TVavrinec/AHS-Automaticke_Herni_Stanoviste/text/sablona-obhaj.pdf

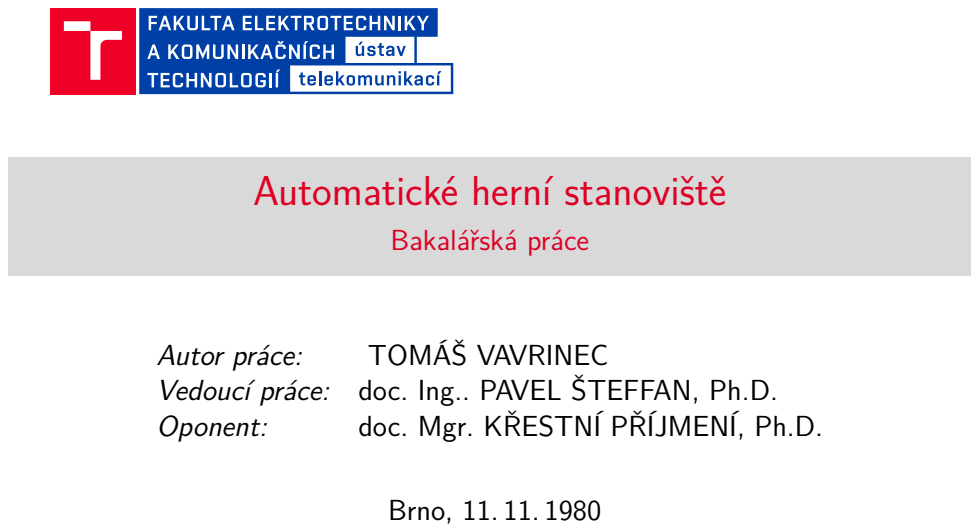
[picture p24: page 1]
Bakalářská práce; Autor práce:; TOMÁŠ VAVRINEC; Oponent:; doc. Mgr. KŘESTNÍ PŘÍJMENÍ, Ph.D.; Brno, 11. 11. 1980

Automatické herní stanoviště

Vedoucí práce: doc. Ing.. PAVEL ŠTEFFAN, Ph.D.

## Cíle práce

Nastudovat
Popsat
nastudované
Implementovat
nastudované
nové
Porovnat a vyhodnotit
výsledky
Tomáš Vavrinec | Automatické herní stanoviště | 1 / 7

## Klíčové nástroje

### Pro práci je klíčový Eulerův vzorec

e

jx = cos x + j sin x

Eulerova identita je speciálním případem tohoto vzorce, jestliže dosadíme x = π :

### Eulerova identita

e

jπ = cos π + j sin π,

odkud vyplývá
e

jπ + 1 = 0.

## Plošný spoj

Obrázek znázorňuje model:

Deska
Součástky
Signály
Napájení

## Výsledky

Tab. 1: Výsledky měření mobilních sítí

Technologie | Rychlost stahování [kB/s] Rychlost nahrávání [kB/s]
GPRS (2,5G) | 7,2 | 3,6
UMTS 3G | 48 | 48
HSPA (3,5G) | 1 706 | 720
LTE (4G) | 40 750 | 10 750

## Závěr

# Děkuji za pozornost!

## Otázky oponenta

Jaká je souvislost Vašeho vzorce (1.2) s Maxwellovými rovnicemi v integrálním tvaru?

Již staří Římané . . .
