TVavrinec/AHS-Automaticke_Herni_Stanoviste/text/text/PraktickaCast/img/dojdesci.png

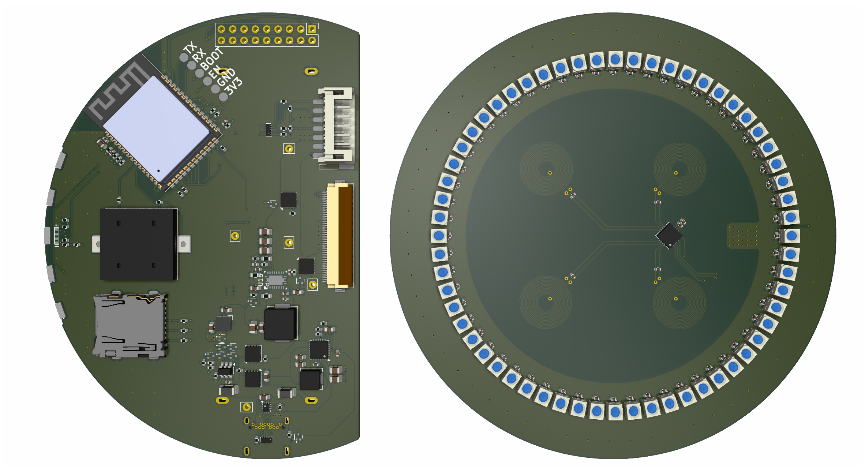
text/text/PraktickaCast/img/dojdesci.png
