TVavrinec/AHS-Automaticke_Herni_Stanoviste/text/text/PraktickaCast/img/osci/trampolina.jpg

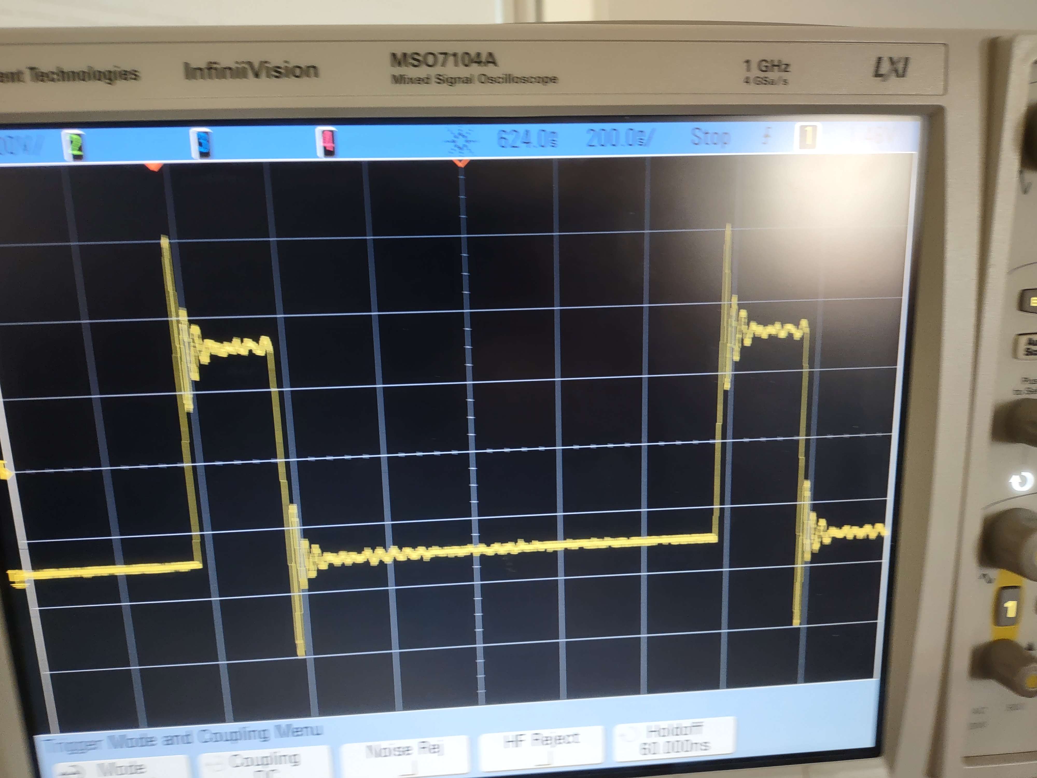
text/text/PraktickaCast/img/osci/trampolina.jpg
