TVavrinec/AHS-Automaticke_Herni_Stanoviste/text/text/PraktickaCast/img/trojdesci.png

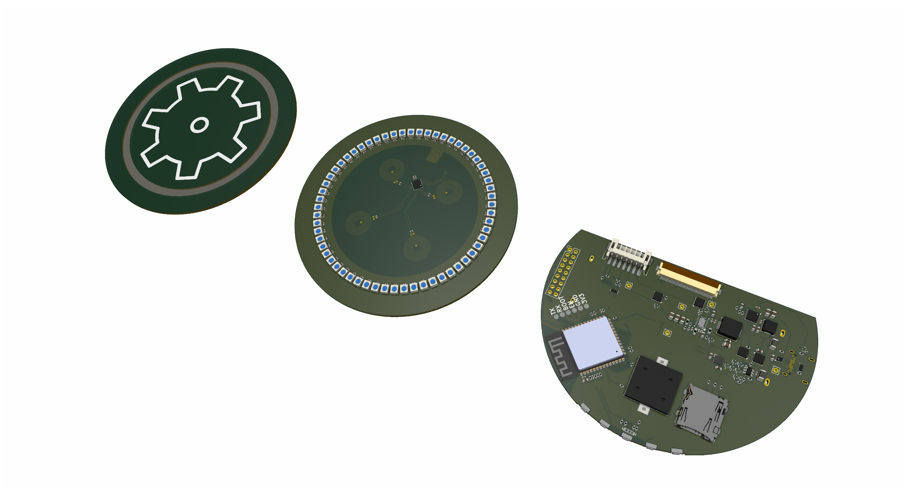
text/text/PraktickaCast/img/trojdesci.png
