TVavrinec/AHS-Automaticke_Herni_Stanoviste/text/text/TeoretickyUvod/AplikaceHernichZarizeni/img/1702085190411.jpg

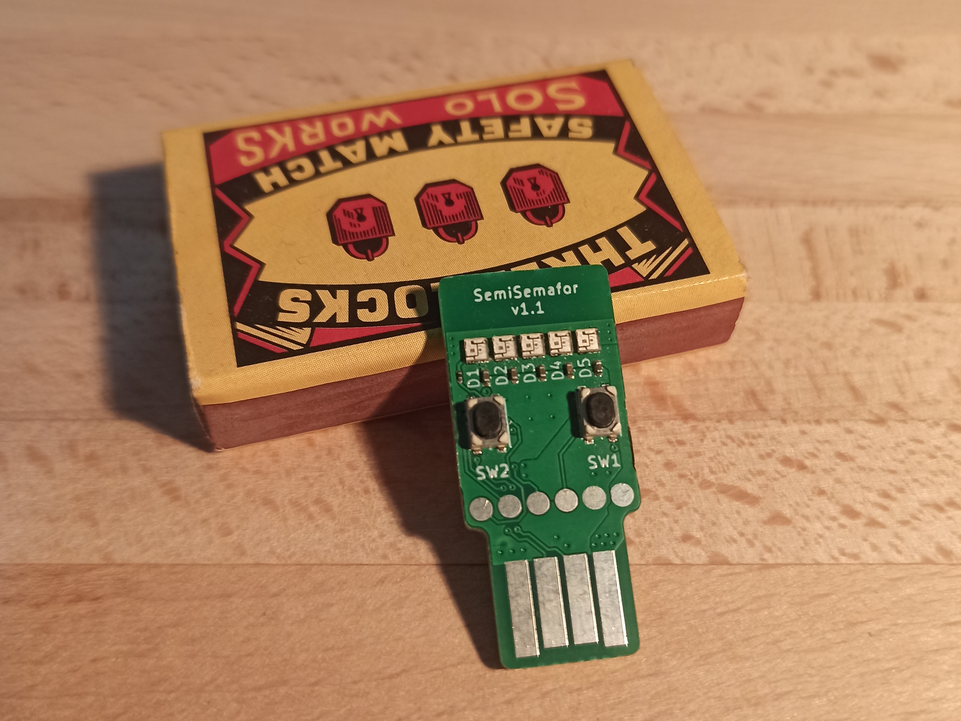
text/text/TeoretickyUvod/AplikaceHernichZarizeni/img/1702085190411.jpg
