TVavrinec/AHS-Automaticke_Herni_Stanoviste/text/text/TeoretickyUvod/AplikaceHernichZarizeni/img/programator.png

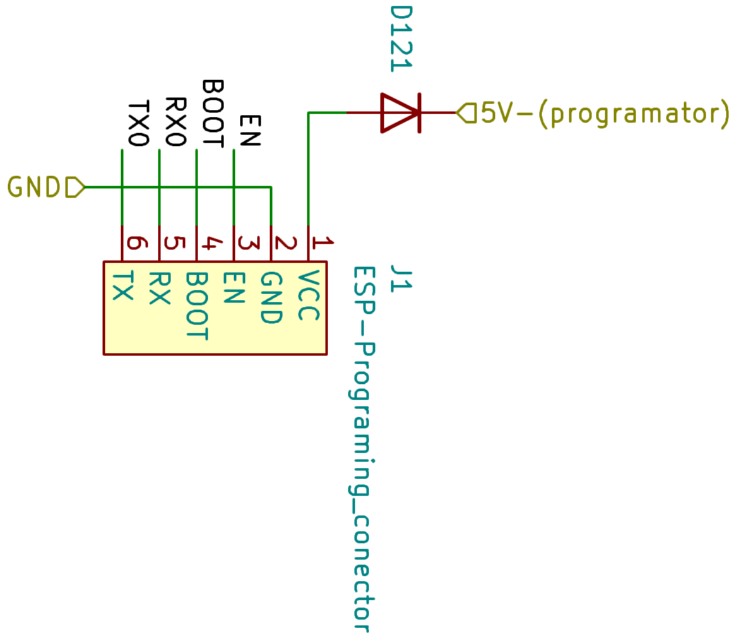
text/text/TeoretickyUvod/AplikaceHernichZarizeni/img/programator.png
