TVavrinec/AHS-Automaticke_Herni_Stanoviste/text/text/PraktickaCast/sch/ZakladniElektronika.pdf

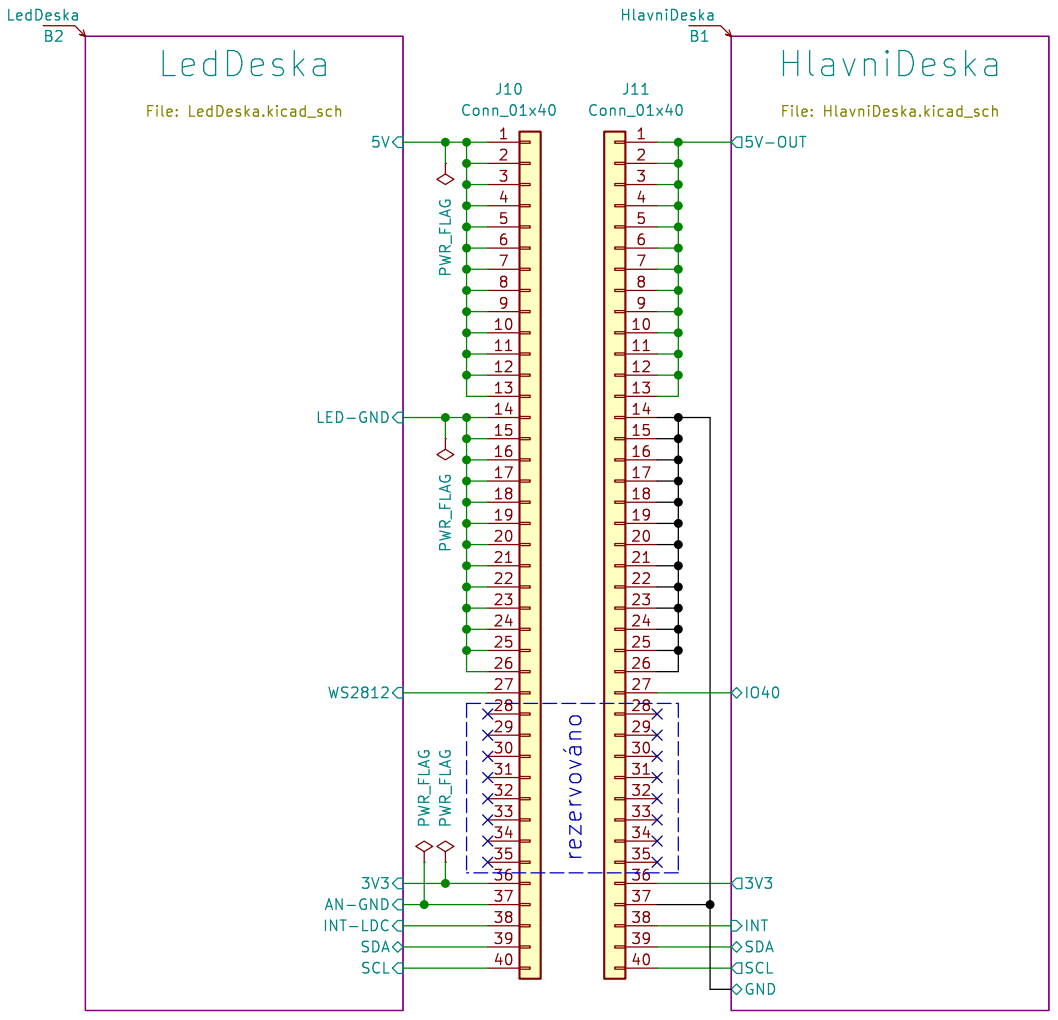
[picture p33: page 1]

Id: 1/12 Title: File: ZakladniElektronika.kicad_sch Sheet: /

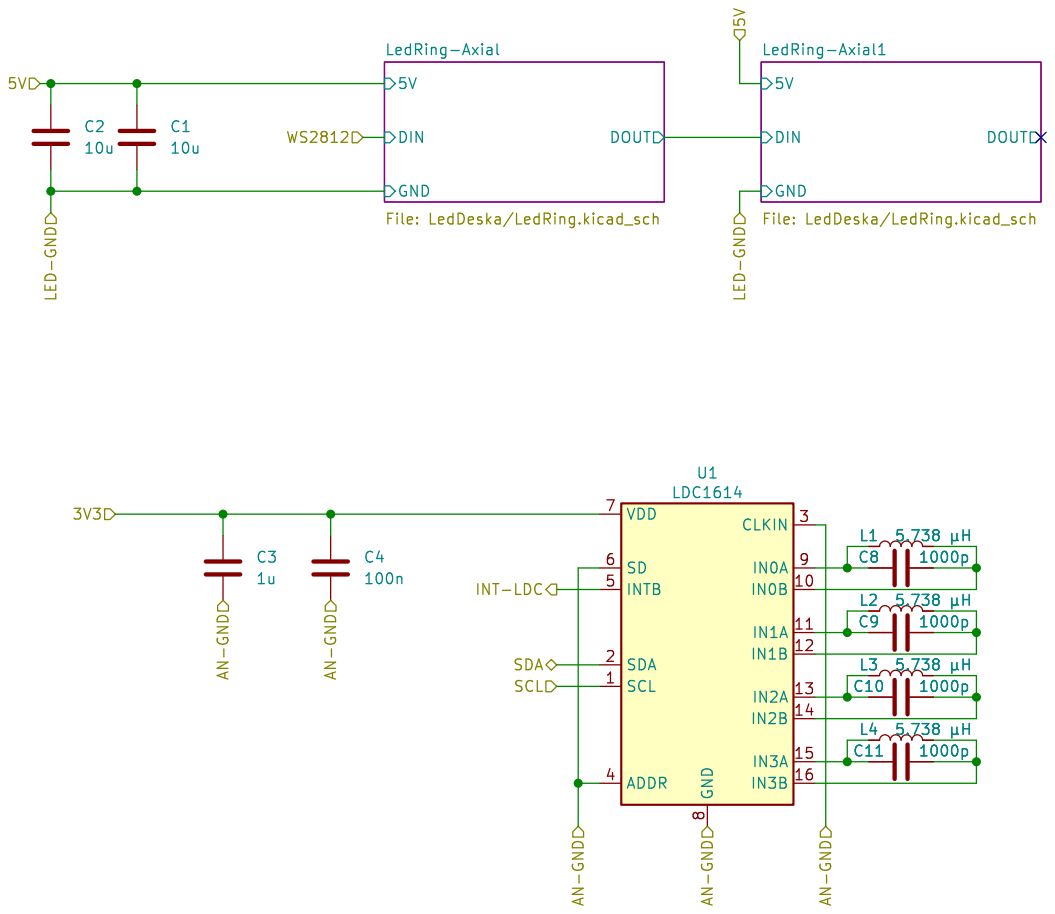
[picture p34: page 2]

LedRing-Axial1 File: LedDeska/LedRing.kicad_sch C4

Id: 2/12 Title: File: LedDeska.kicad_sch Sheet: /LedDeska/

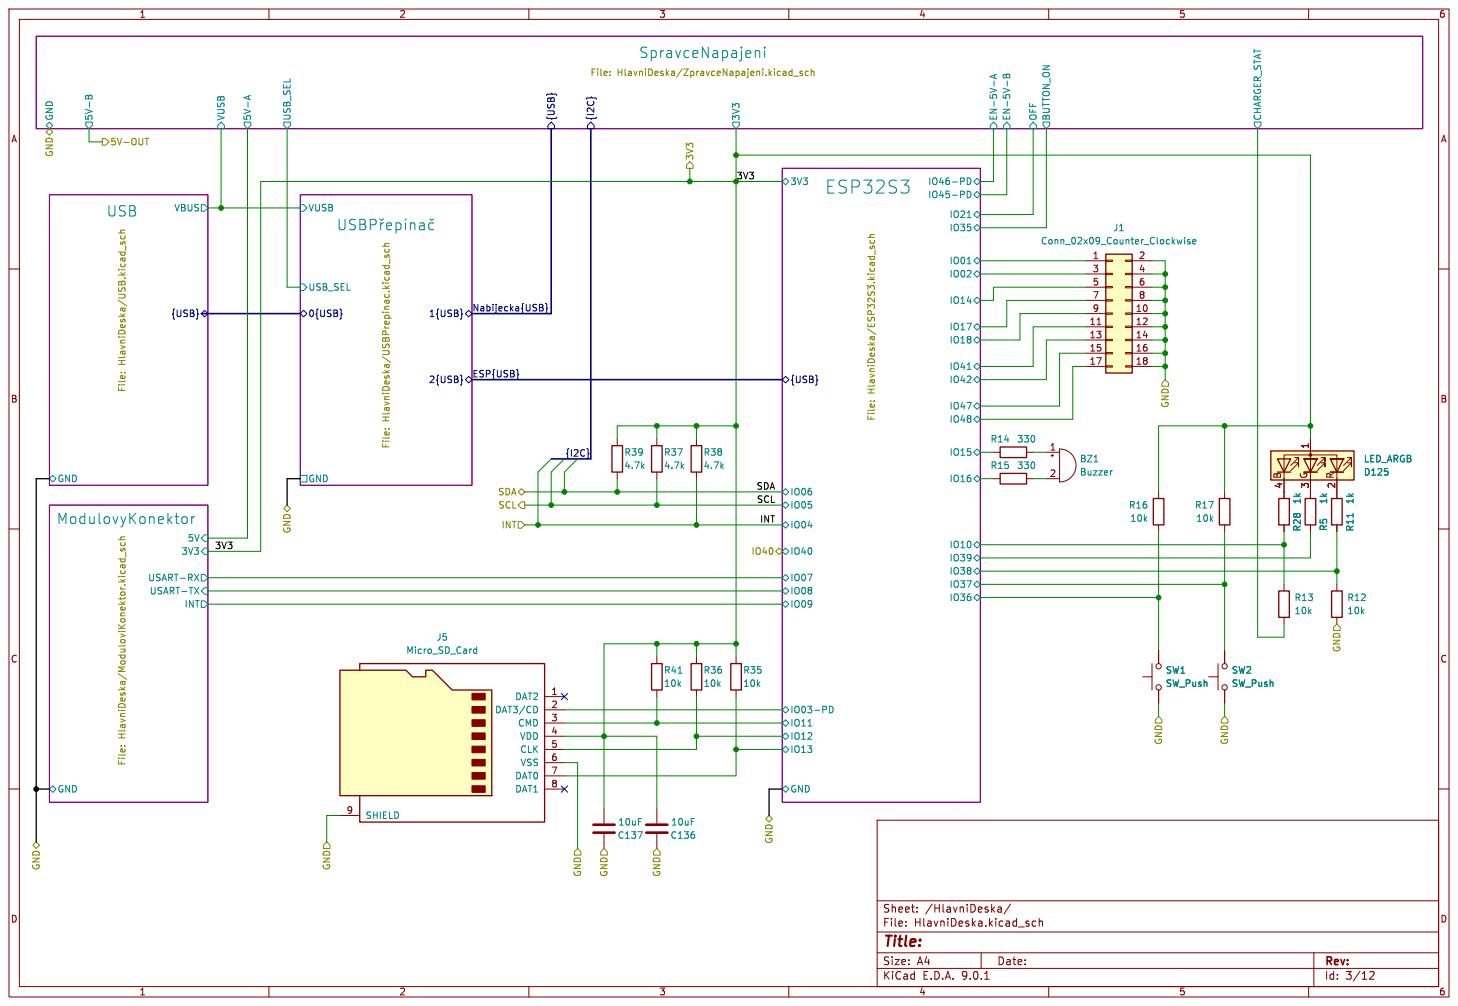
[picture p35: page 3]

USART-RX USART-TX

Id: 3/12 Title: File: HlavniDeska.kicad_sch Sheet: /HlavniDeska/

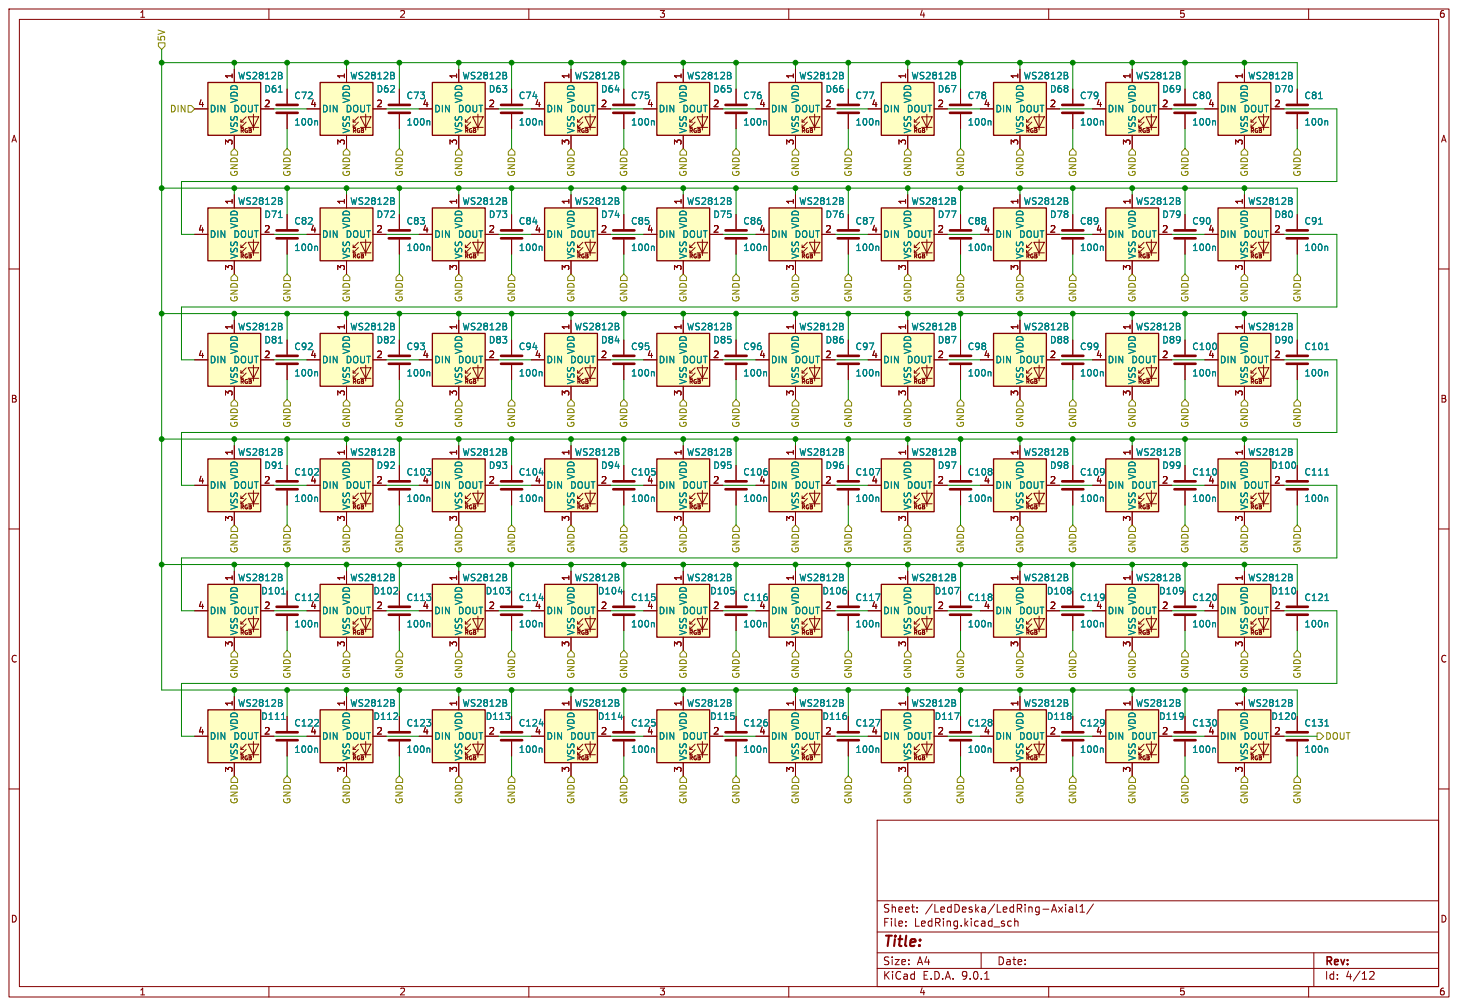
[picture p36: page 4]

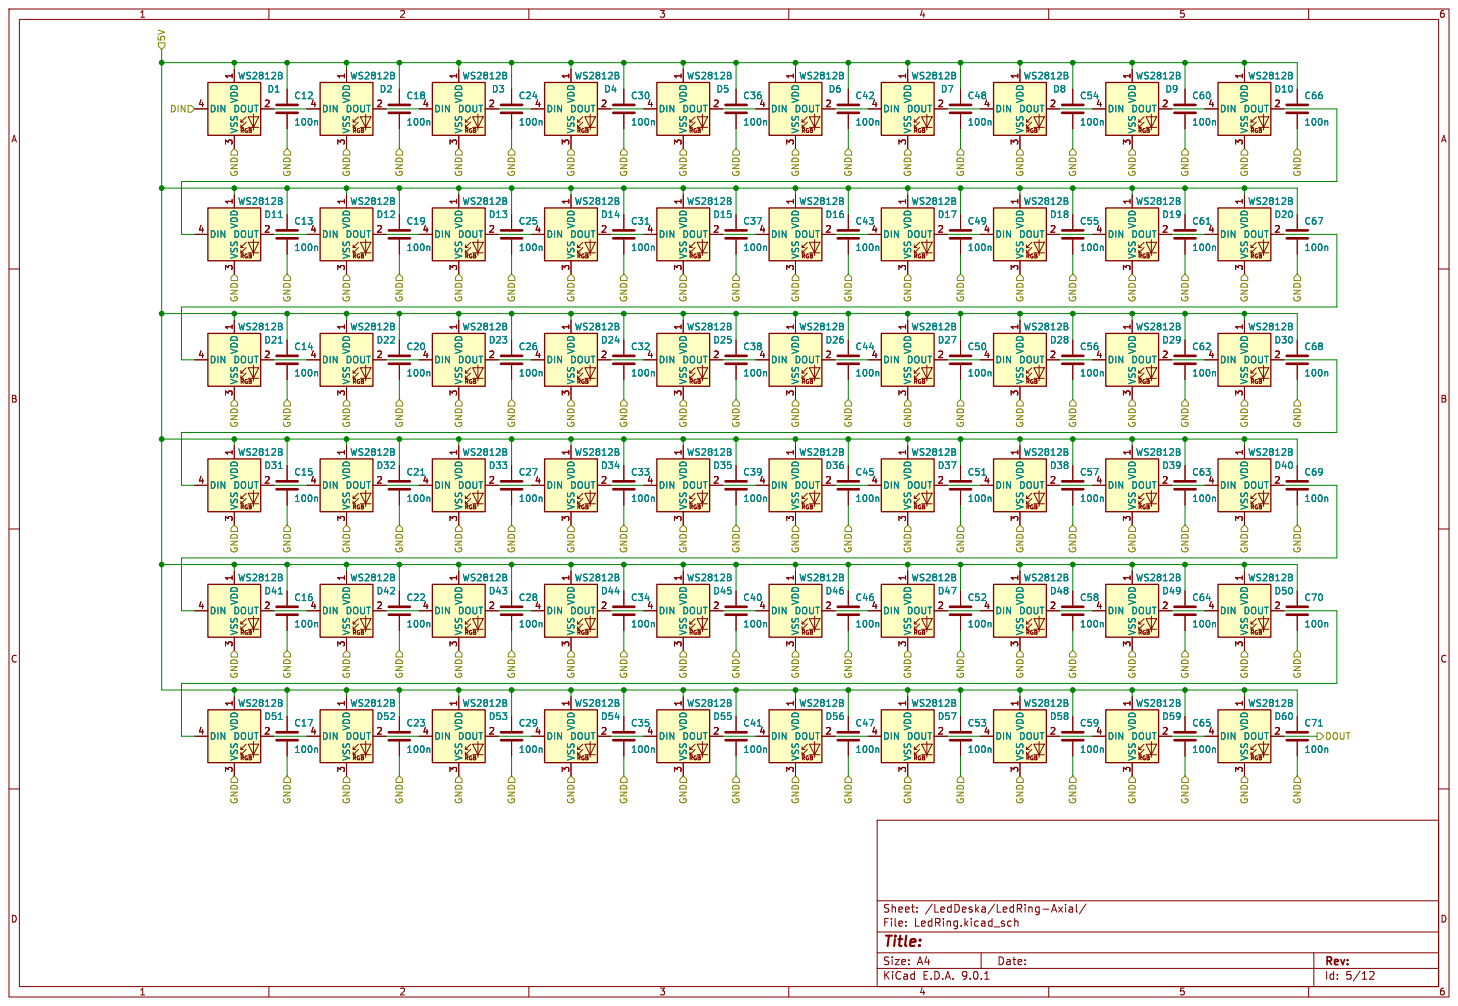
[picture p37: page 5]

3 DOUT 2D21 WS2812B GND GND GND GND GND GND GND GND GND GND GND GND GND GND GND GND GND GND GND GND GND GND GND GND GND GND GND GND GND GND GND GND GND GND GND GND GND GND GND GND GND GND GND GND GND GND GND GND GND GND GND GND GND GND GND GND GND GND GND GND GND GND GND GND GND GND GND GND GND GND GND GND GND GND GND GND GND GND GND GND GND GND GND GND GND GND GND GND GND GND GND GND GND GND GND GND GND GND GND GND

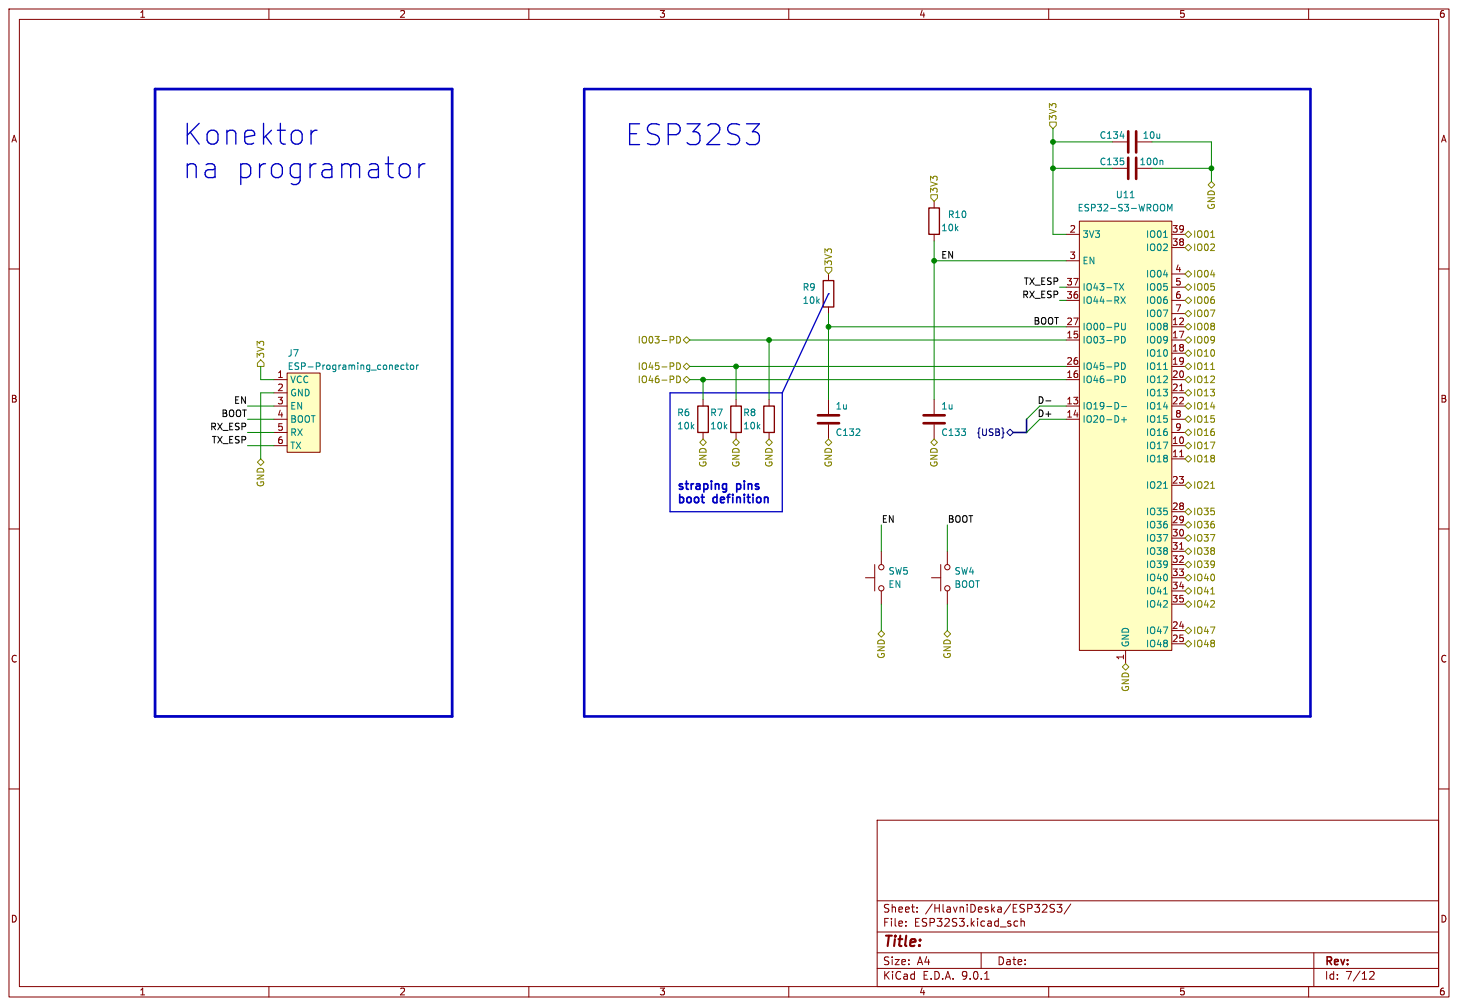
[picture p38: page 6]

Id: 7/12 Title: File: ESP32S3.kicad_sch Sheet: /HlavniDeska/ESP32S3/

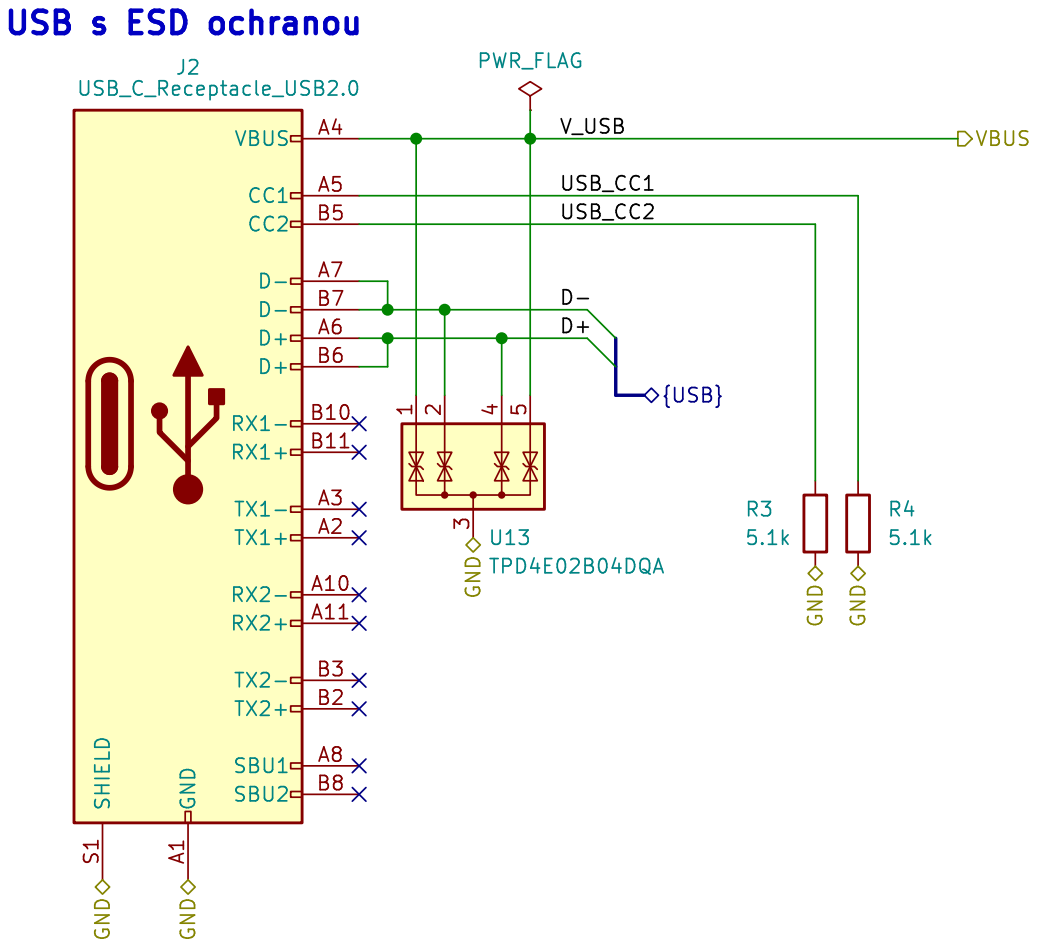
[picture p39: page 7]

Id: 8/12 Title: File: USB.kicad_sch Sheet: /HlavniDeska/USB/ R4

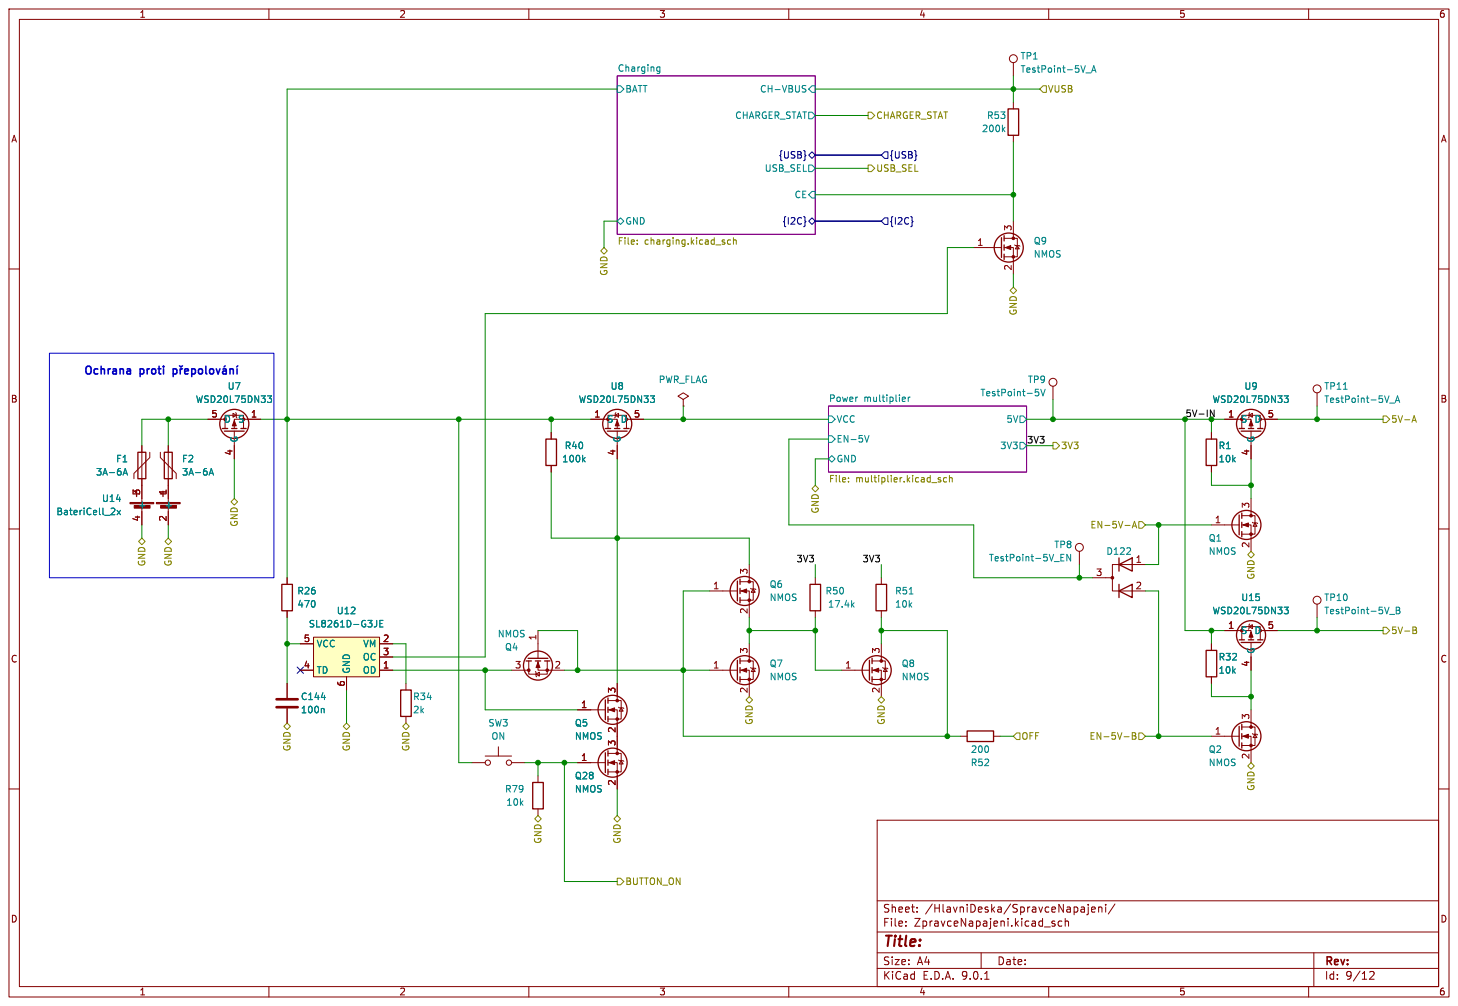
[picture p40: page 8]

{USB} CHARGER_STAT CE Charging File: charging.kicad_sch

Power multiplier File: multiplier.kicad_sch BATT GND

3V3 VCC
Id: 9/12 Title: File: ZpravceNapajeni.kicad_sch Sheet: /HlavniDeska/SpravceNapajeni/ GND

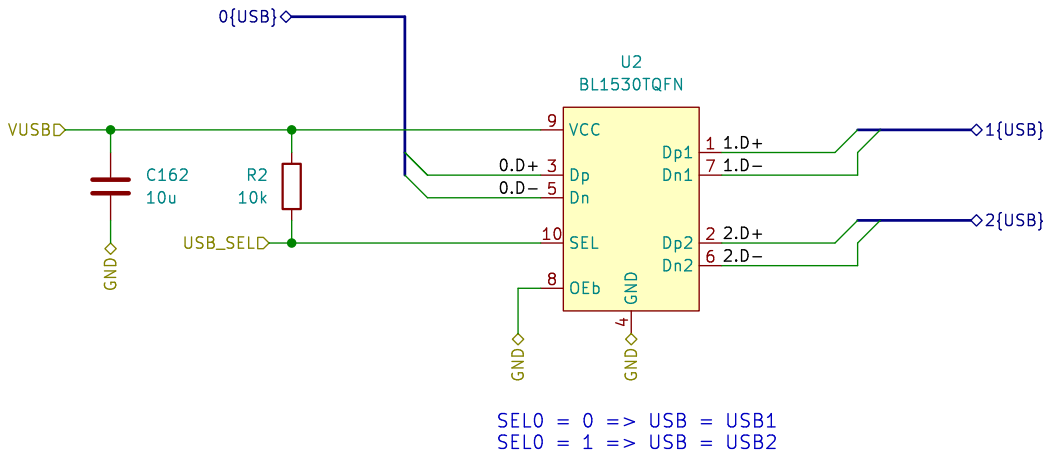
[picture p41: page 9]

Id: 15/12 Title: File: USBPrepinac.kicad_sch Sheet: þÿ/HlavniDeska/USBPYepína

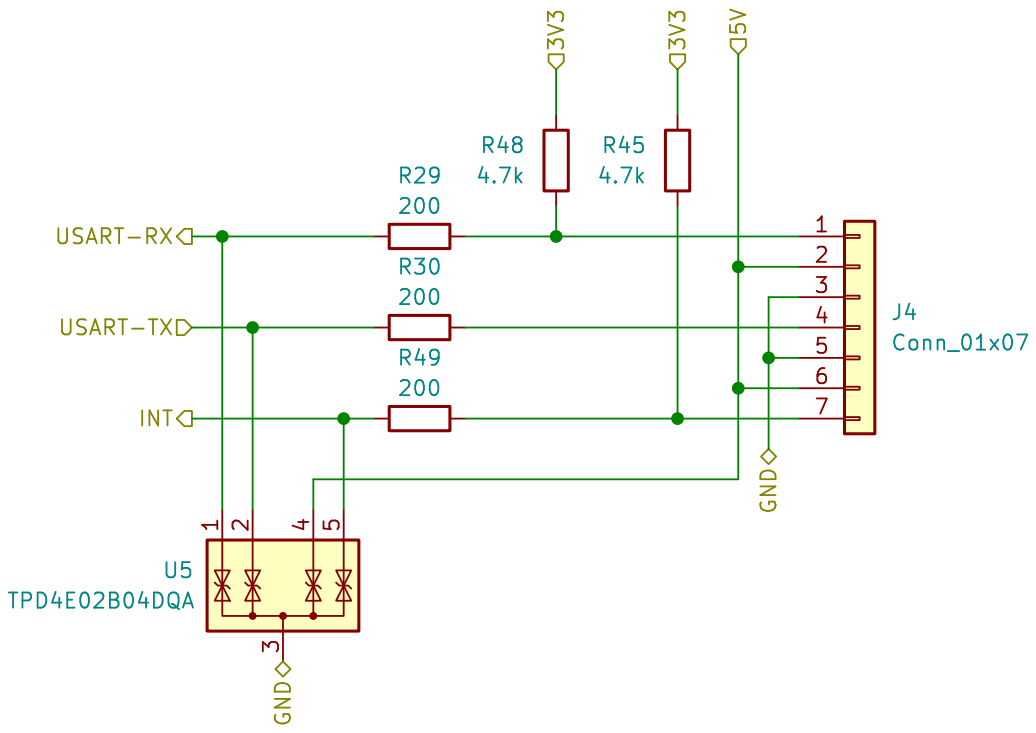
[picture p42: page 10]

Id: 22/12 Title: File: ModuloviKonektor.kicad_sch Sheet: /HlavniDeska/ModulovyKonektor/

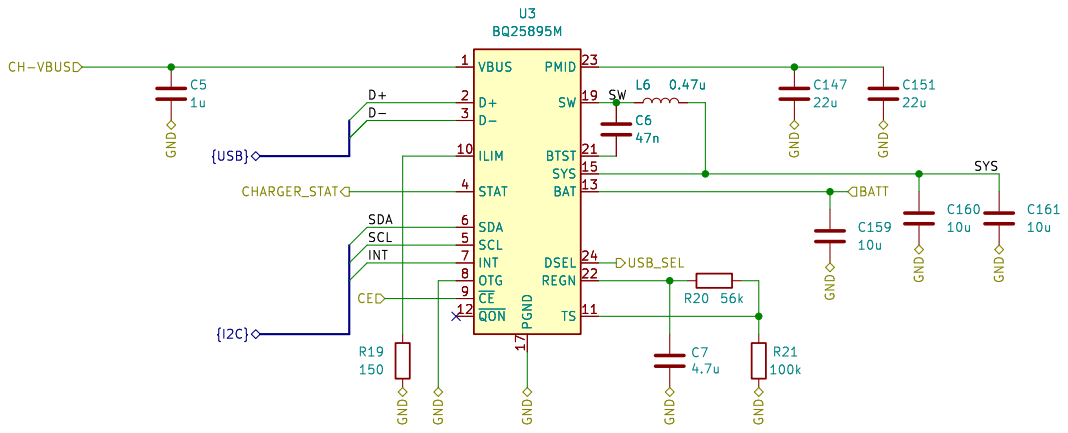
[picture p43: page 11]

Id: 6/12 Title: File: charging.kicad_sch Sheet: /HlavniDeska/SpravceNapajeni/Charging/

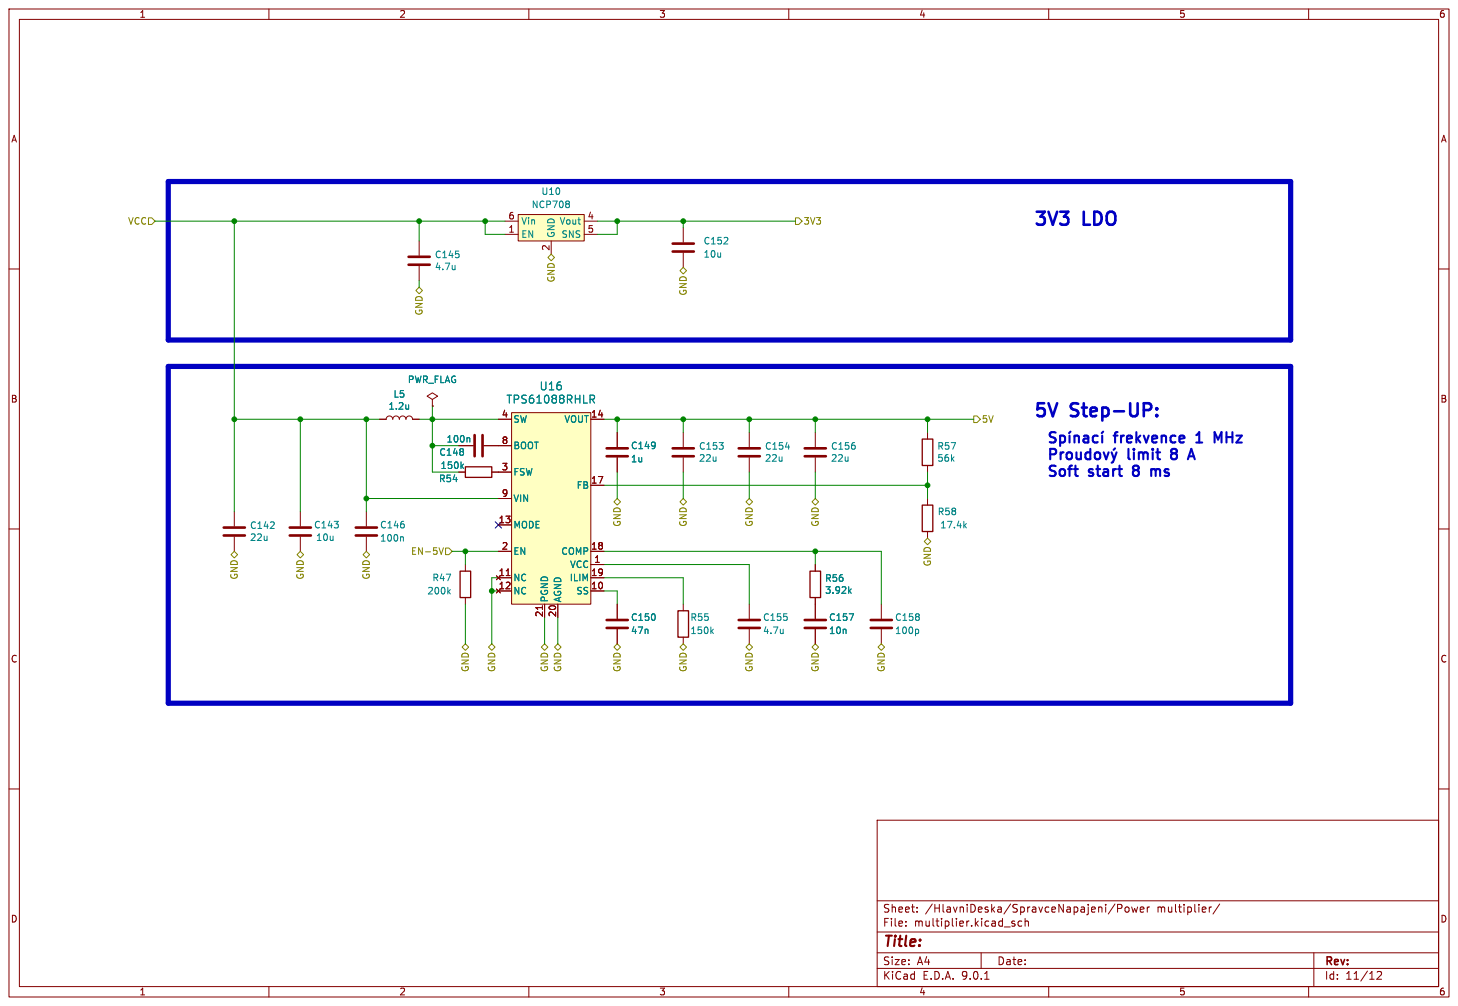
[picture p44: page 12]
