TVavrinec/AHS-Automaticke_Herni_Stanoviste/text/text/PraktickaCast/sch/SemiSemafor-v1.1.pdf

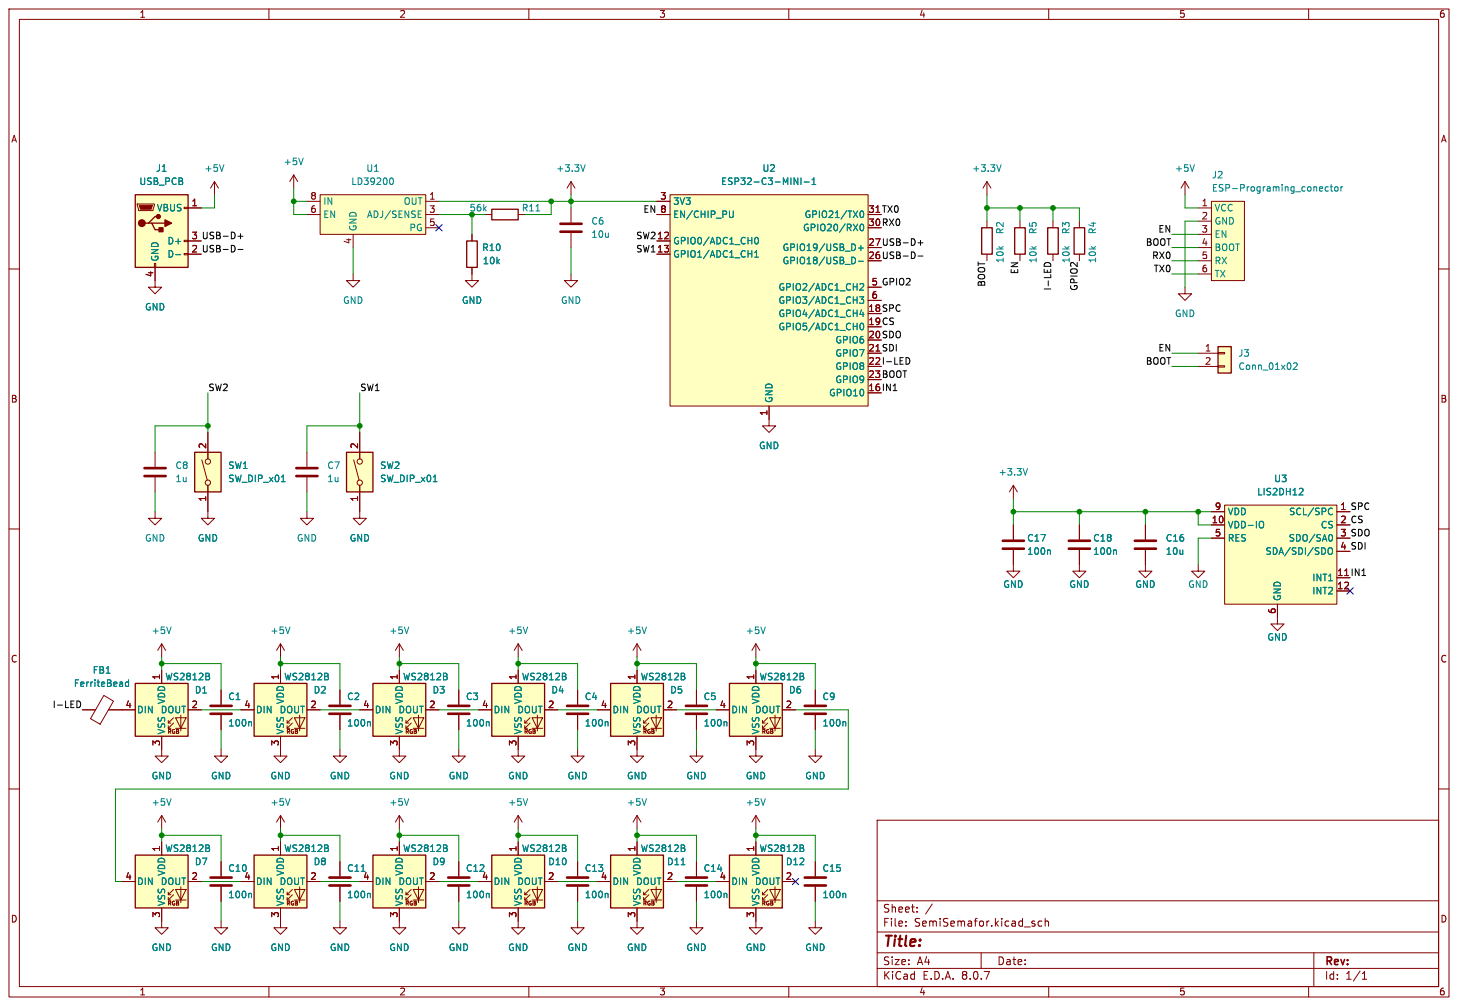
[picture p45: page 1]

VCC 1 GND 2 EN 3 BOOT 4 RX 5 TX 6

3 DIN 4 GND GND GND GND GND GND

6 VDD 9 U3
LIS2DH12SCL/SPC 1 VDD-IO 10
SCL/SPC 1 VDD-IO 10

3 DIN 4 GND GND GND GND

3 DIN 4 GND GND GND
