TVavrinec/AHS-Automaticke_Herni_Stanoviste/text/text/TeoretickyUvod/AplikaceHernichZarizeni/diagram/zanoreni_0.pdf

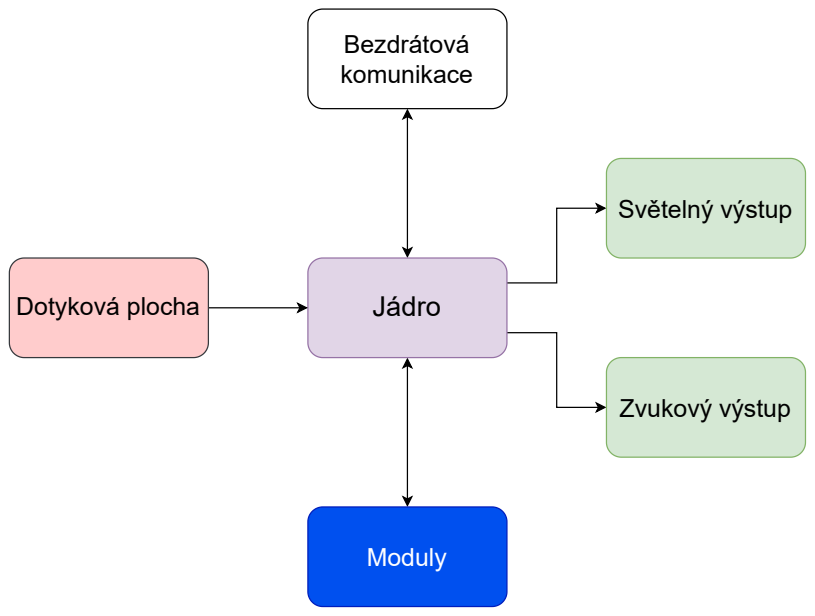
[picture p46: page 1]
Dotyková plocha; Jádro; Světelný výstup; Zvukový výstup; Bezdrátová komunikace; Moduly
