TVavrinec/AHS-Automaticke_Herni_Stanoviste/text/text/TeoretickyUvod/AplikaceHernichZarizeni/diagram/zanoreni_1.pdf

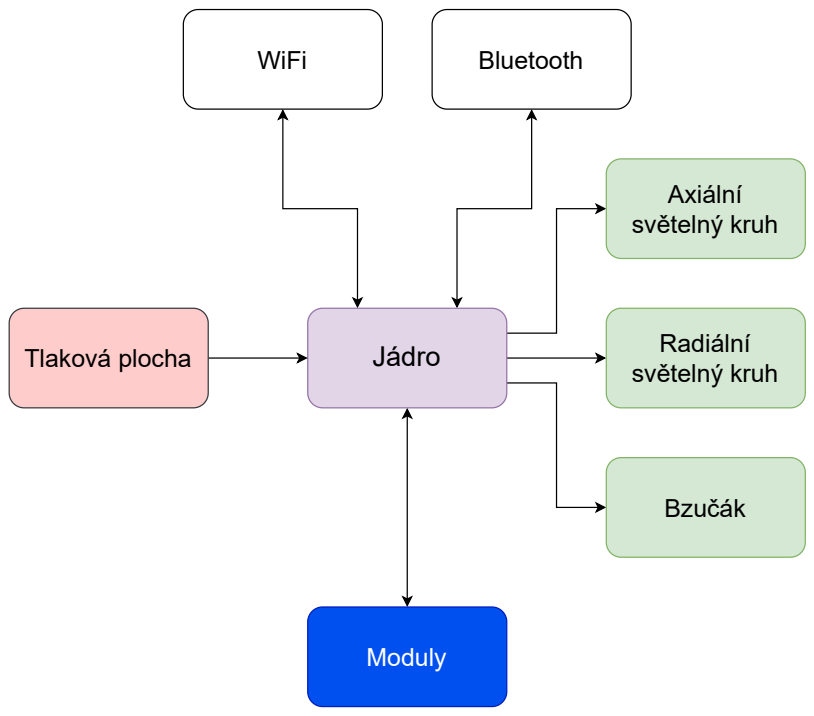
[picture p47: page 1]
Tlaková plocha; Jádro; Axiální světelný kruh; Radiální světelný kruh; Bzučák; WiFi; Bluetooth; Moduly
