TVavrinec/AHS-Automaticke_Herni_Stanoviste/text/text/TeoretickyUvod/AplikaceHernichZarizeni/diagram/Dvirka.drawio.pdf

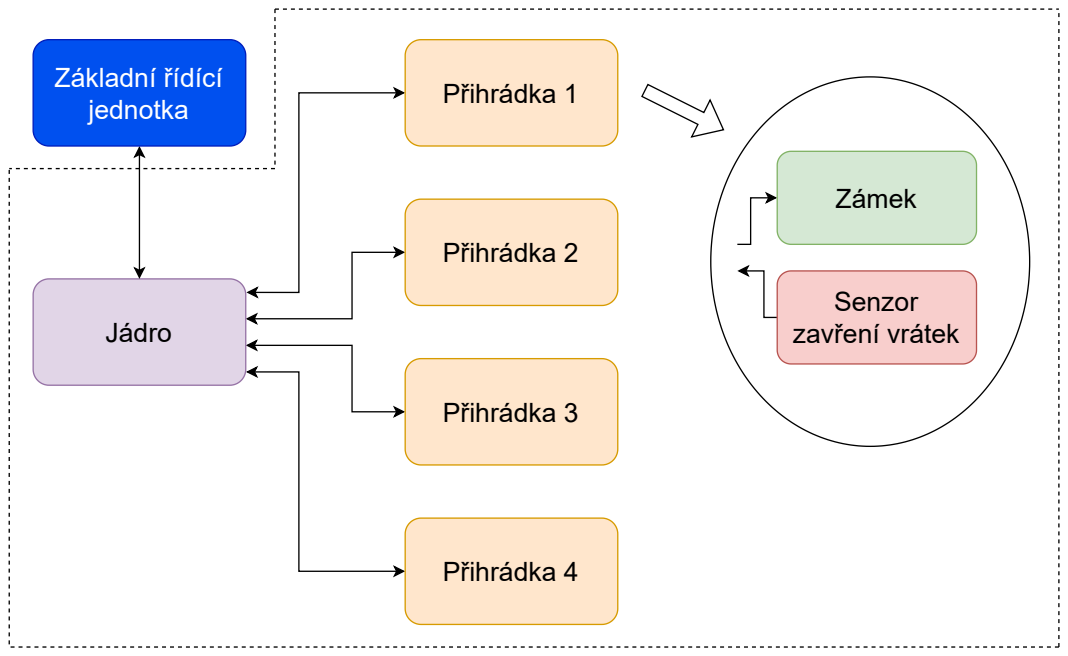
[picture p48: page 1]
Jádro; Přihrádka 1; Přihrádka 2; Přihrádka 3; Přihrádka 4; Základní řídící jednotka; Zámek; Senzor zavření vrátek
