TVavrinec/AHS-Automaticke_Herni_Stanoviste/text/text/PraktickaCast/sch/SemiSemafor-V1.0.pdf

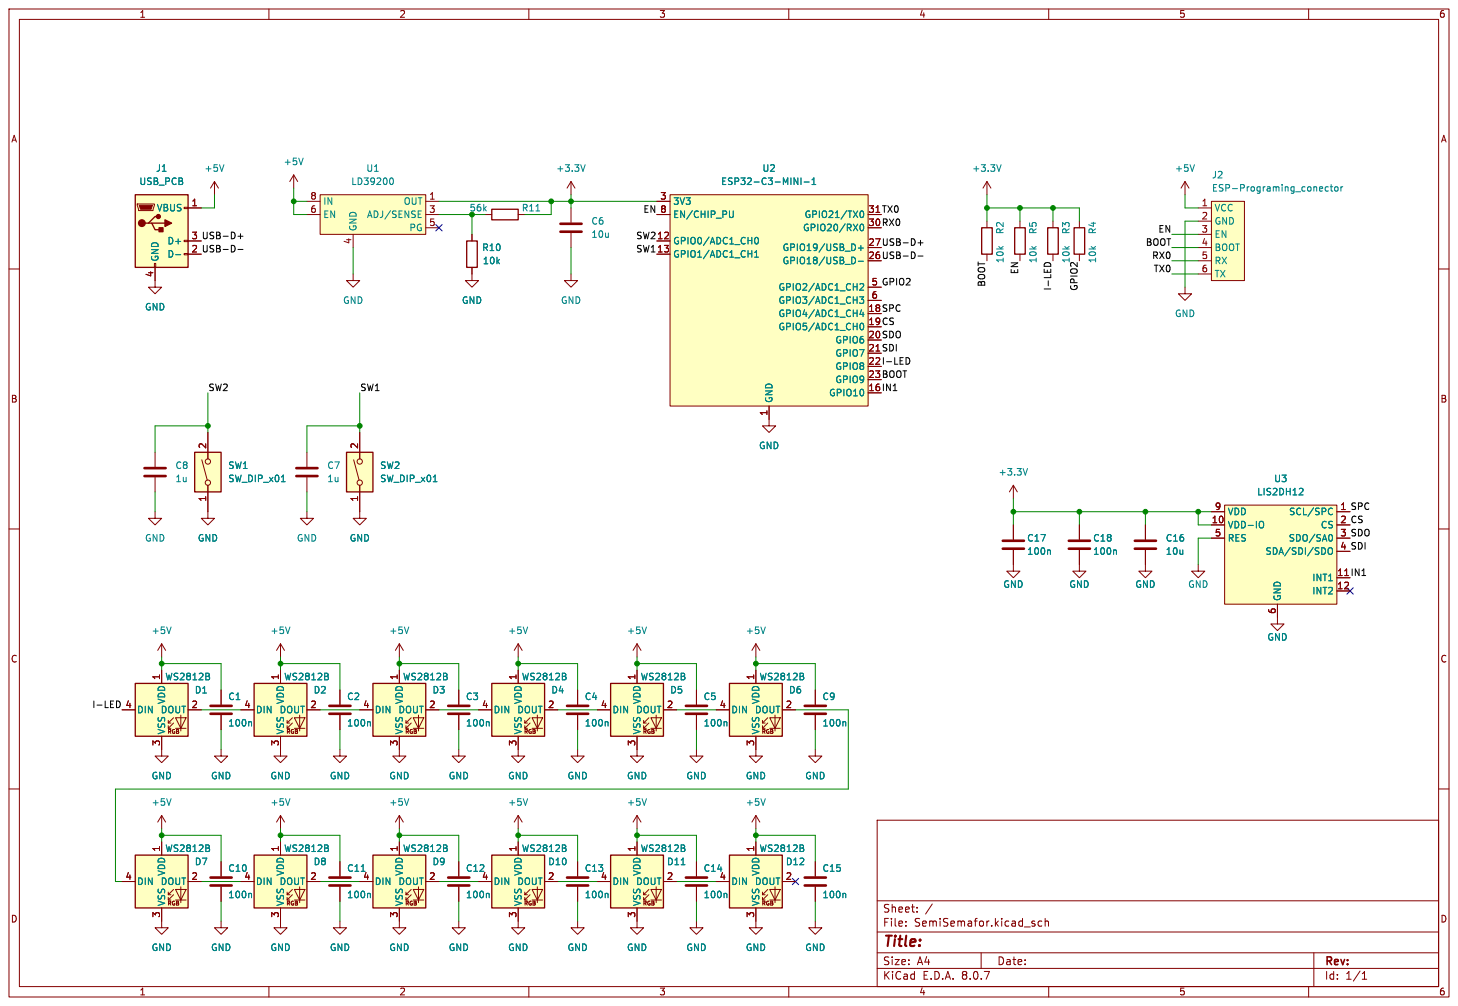
[picture p49: page 1]

LIS2DH12 VCC 1 GND 2 EN 3 BOOT 4 RX 5 TX 6

6 VDD 9 U3
LIS2DH12SCL/SPC 1 VDD-IO 10
SCL/SPC 1 VDD-IO 10

Id: 1/1 Title: File: SemiSemafor.kicad_sch Sheet: / C5

3 DIN 4 GND GND GND GND

3 DIN 4 D9 WS2812B GND GND GND
