TVavrinec/AHS-Automaticke_Herni_Stanoviste/text/text/PraktickaCast/sch/power_manager.kicad_sch

## KiCad design text/text/PraktickaCast/sch/power_manager.kicad_sch (2025-06-01)

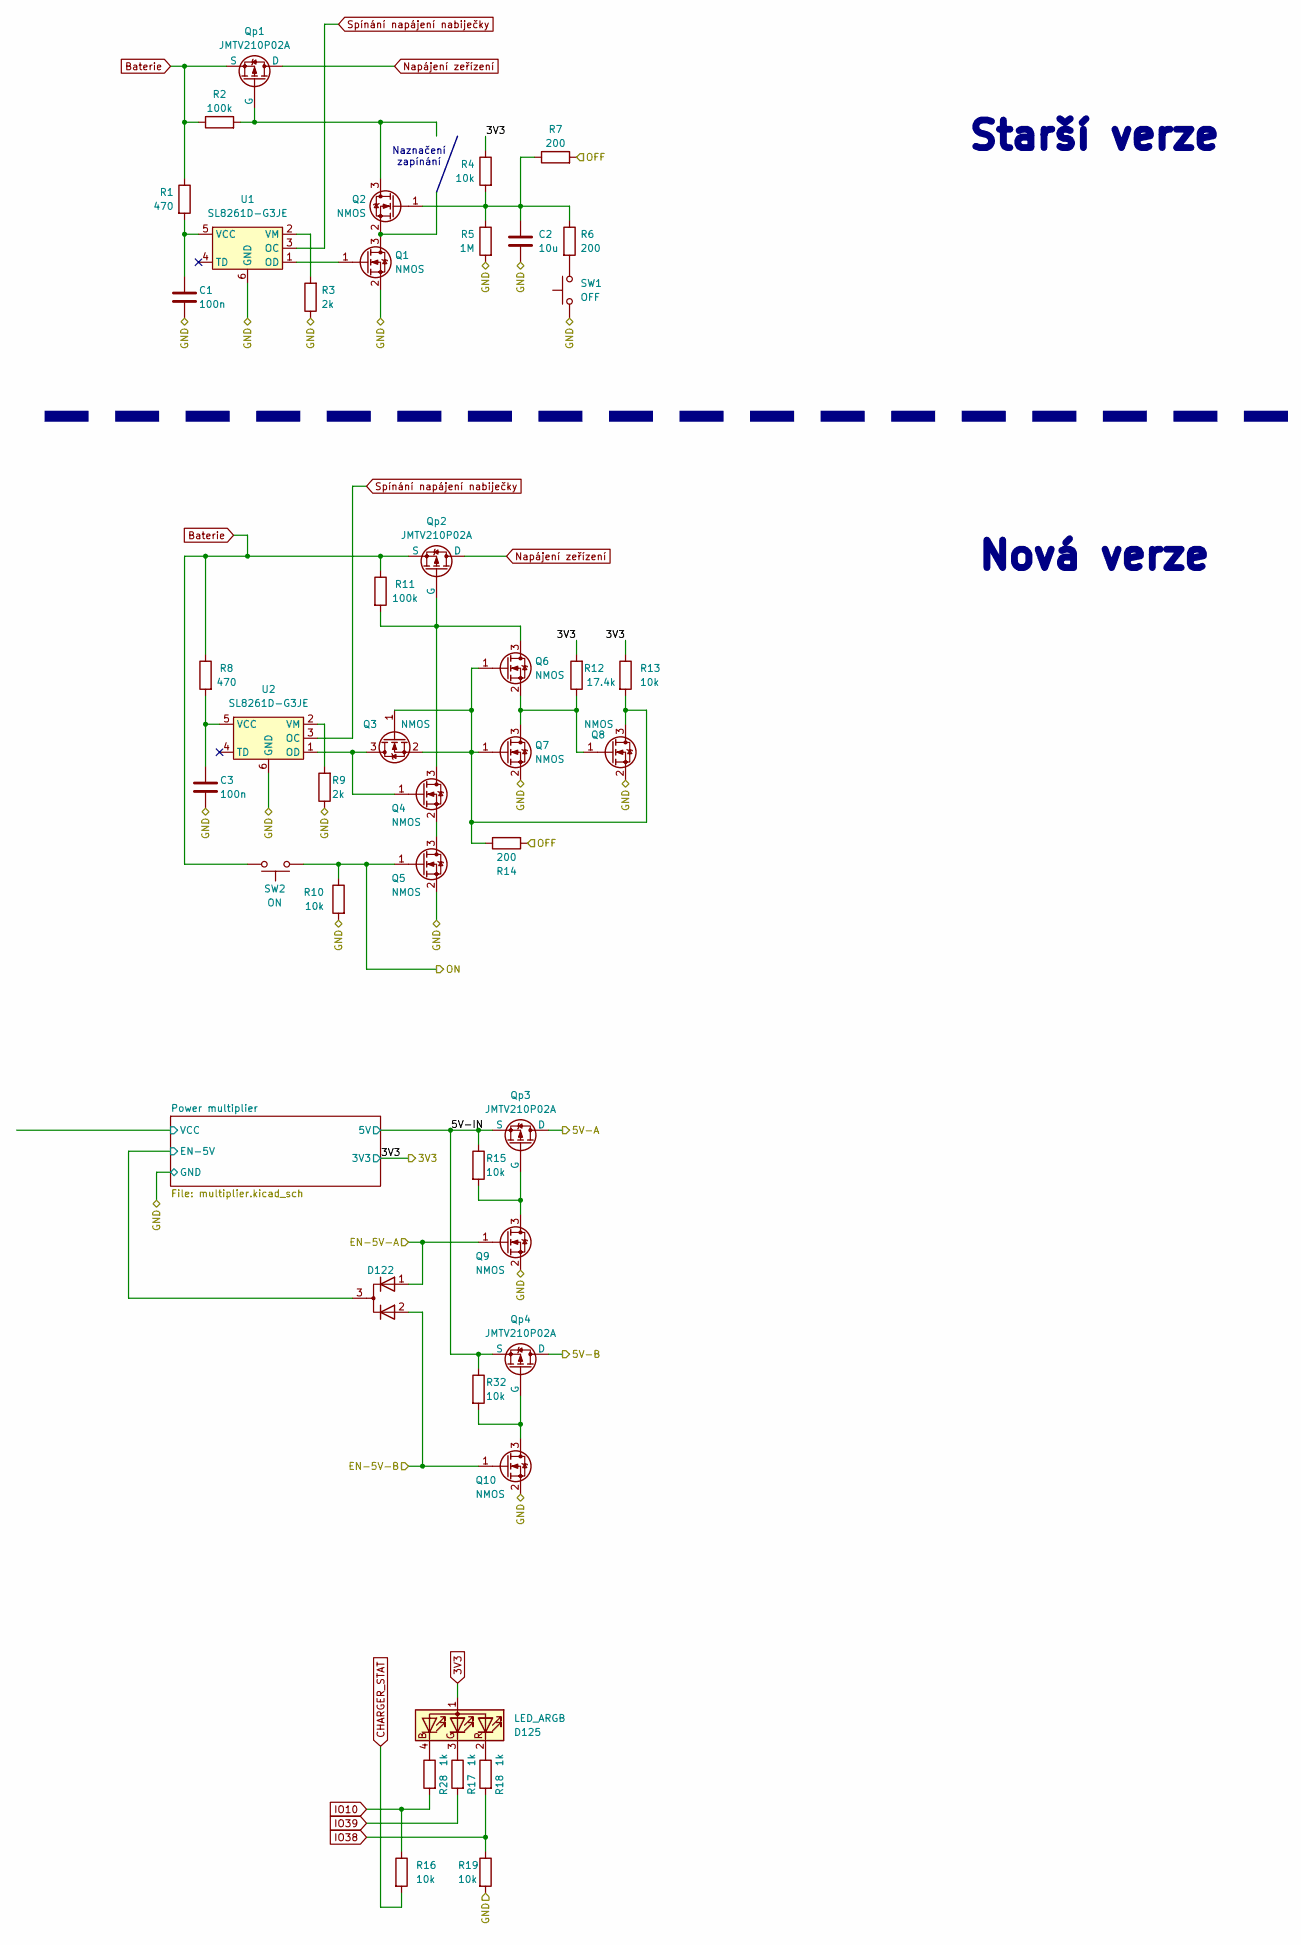
[picture p56: schematic power_manager.kicad_sch, part in row 1, column 1]

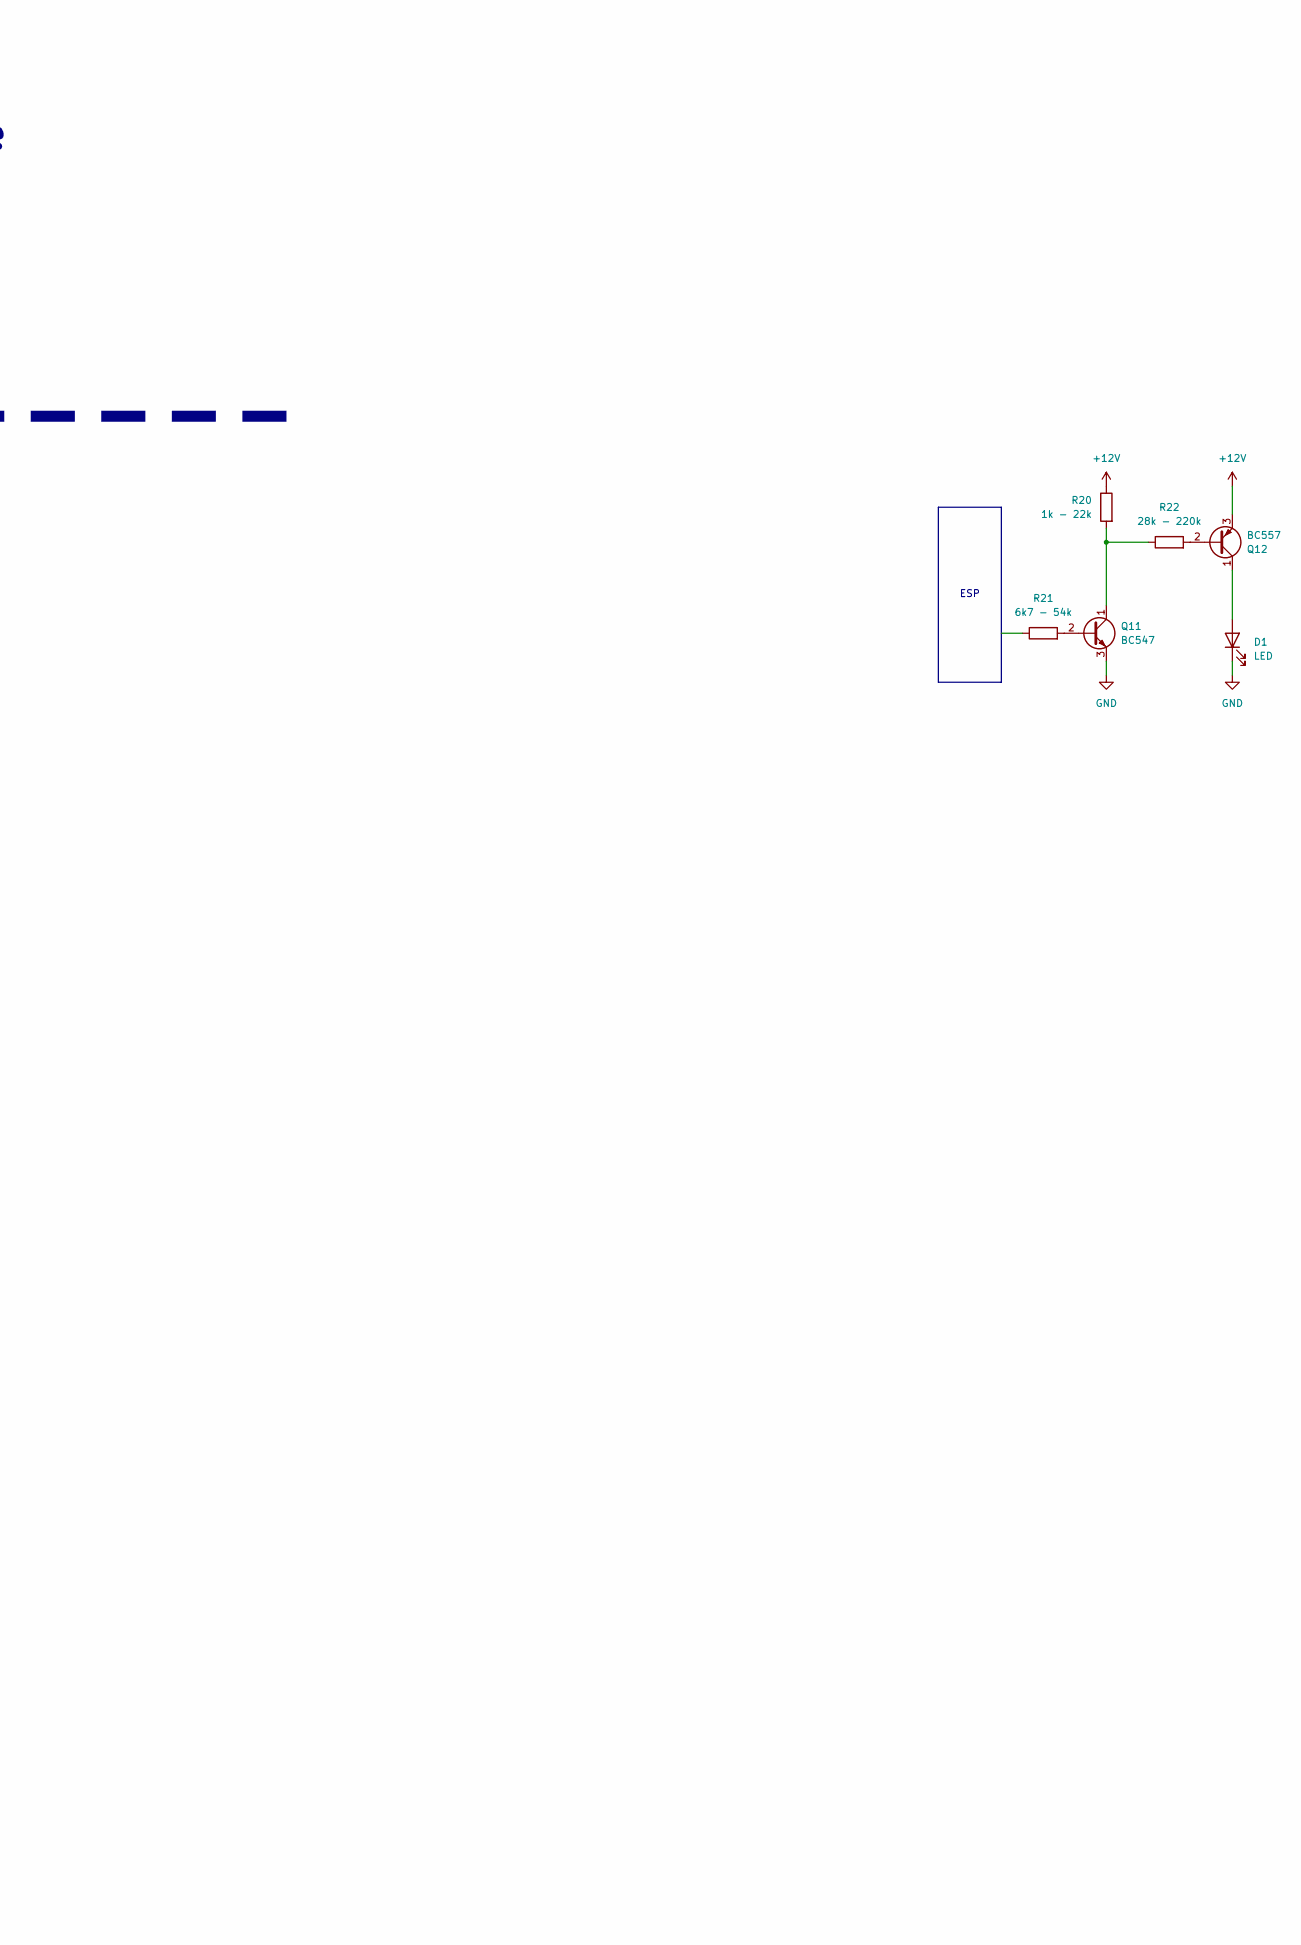
[picture p57: schematic power_manager.kicad_sch, part in row 1, column 2]

Parts:
C1, C3: 100n; C_0402_1005Metric; LCSC C1525
C2: 10u; C_0603_1608Metric; LCSC C96446
D1: LED
D122: D_Dual_CommonCathode_AAK_Parallel; SOT-723; LCSC C896182
D125: LED_ARGB; XL-3806RGBC-4L; LCSC C2843779
Q1, Q2: NMOS; SOT-723; LCSC C504051
Q3, Q4, Q5, Q6, Q7, Q8, Q9, Q10: NMOS; SOT-723; LCSC C2912553
Q11: BC547; TO-92_Inline
Q12: BC557; TO-92_Inline
Qp1, Qp2, Qp3, Qp4: JMTV210P02A
R1, R8: 470; R_0402_1005Metric; LCSC C25117
R2, R11: 100k; R_0402_1005Metric; LCSC C25741
R3, R9: 2k; R_0402_1005Metric; LCSC C4109
R4, R10, R13, R15, R16, R19, R32: 10k; R_0402_1005Metric; LCSC C25744
R5: 1M; R_0402_1005Metric; LCSC C26083
R6, R7, R14: 200; R_0402_1005Metric; LCSC C25087
R12: 17.4k; R_0402_1005Metric; LCSC C208810
R17, R18, R28: 1k; R_0402_1005Metric; LCSC C11702
R20: 1k - 22k
R21: 6k7 - 54k
R22: 28k - 220k
SW1: OFF; SW_Push_1P1T_NO_Vertical_Wuerth_434133025816; LCSC C127488
SW2: ON; SW_Push_1P1T_NO_Vertical_Wuerth_434133025816; LCSC C115360
U1, U2: SL8261D-G3JE; SOT-23-6; LCSC C5186027

Connections:
3V3: D125.1 (A), R4.1, R12.2, R13.1
5V-A: Qp3.1 (D)
5V-B: Qp4.1 (D)
5V-IN: Qp3.3 (S), Qp4.3 (S), R15.1, R32.1
+12V: Q12.3 (E), R20.1
Baterie: Qp1.3 (S), Qp2.3 (S), R1.1, R2.1, R8.1, R11.1, SW2.1
CHARGER_STAT: R16.2
EN-5V: D122.3 (A)
EN-5V-A: D122.1 (K), Q9.1 (G)
EN-5V-B: D122.2 (K), Q10.1 (G)
GND: C1.2, C2.2, C3.2, D1.1 (K), Q1.2 (S), Q5.2 (S), Q7.2 (S), Q8.2 (S), Q9.2 (S), Q10.2 (S), Q11.3 (E), R3.1, R5.2, R9.1, R10.2, R19.2, SW1.1, U1.6 (GND), U2.6 (GND)
IO10: R16.1, R28.2
IO38: R18.2, R19.1
IO39: R17.2
Napájení zeřízení: Qp1.1 (D), Qp2.1 (D)
unnamed: C1.1, R1.2, U1.5 (VCC)
unnamed: C2.1, Q2.1 (G), R4.2, R5.1, R6.1, R7.1
unnamed: C3.1, R8.2, U2.5 (VCC)
unnamed: D1.2 (A), Q12.1 (C)
unnamed: D125.2 (RK), R18.1
unnamed: D125.3 (GK), R17.1
unnamed: D125.4 (BK), R28.1
unnamed: Q1.1 (G), U1.1 (OD)
unnamed: Q1.3 (D), Q2.2 (S)
unnamed: Q2.3 (D), Qp1.2 (G), R2.2
unnamed: Q3.1 (G), Q3.2 (S), Q6.1 (G), Q7.1 (G), Q8.3 (D), R13.2, R14.1
unnamed: Q3.3 (D), Q4.1 (G), U2.1 (OD)
unnamed: Q4.2 (S), Q5.3 (D)
unnamed: Q4.3 (D), Q6.3 (D), Qp2.2 (G), R11.2
unnamed: Q6.2 (S), Q7.3 (D), Q8.1 (G), R12.1
unnamed: Q9.3 (D), Qp3.2 (G), R15.2
unnamed: Q10.3 (D), Qp4.2 (G), R32.2
unnamed: Q11.1 (C), R20.2, R22.1
unnamed: Q11.2 (B), R21.2
unnamed: Q12.2 (B), R22.2
unnamed: R3.2, U1.2 (VM)
unnamed: R6.2, SW1.2
unnamed: R9.2, U2.2 (VM)
OFF: R7.2, R14.2
ON: Q5.1 (G), R10.1, SW2.2
Spínání napájení nabiječky: U1.3 (OC), U2.3 (OC)

Notes on the sheet:
Naznačení zapínání
Starší verze
ESP
Nová verze
